miguel9554/dce-pfinal/simulaciones/informe/bw.asc

C1: cap; 1000µ
R1: res; 12k
R2: res; 470
RL: res; {RL}
V1: voltage; ""; AC 1
Ven: voltage; {Vcc}
Vep: voltage; {Vcc}
Vin: voltage; {V1}
Vip: voltage; {V1}
X7: amplificador
Named nets: Vcc, -Vcc, V-, 0, Vin, V+, Vo
.param V1=15 Vcc=30
.param RL=8
.ac dec 1000 1 200k
