miguel9554/dce-pfinal/simulaciones/informe/eficiencia.asc

C1: cap; 1000µ
R1: res; 12k
R2: res; 470
RL: res; {RL}
V1: voltage; SINE(0 {Vinpp/2} {fin})
Ven: voltage; {Vcc}
Vep: voltage; {Vcc}
Vin: voltage; {V1}
Vip: voltage; {V1}
X7: amplificador
Named nets: Vcc, -Vcc, V-, 0, Vin, V+, Vo
.param N_cycles_show=1 N_cycles_wait=10
.param Vinpp=2 fin=100
.param V1=15 Vcc=30
.param RL=8
.tran 0 {(N_cycles_wait+N_cycles_show)/fin} {N_cycles_wait/fin} {1/(fin*10e3)}
.meas TRAN P_Vep AVG -V(vcc)*I(Vep) FROM 0
.meas TRAN P_Ven AVG V(-vcc)*I(Ven) FROM 0
.meas TRAN P_Vip AVG -V(V+)*I(Vip) FROM 0
.meas TRAN P_Vin AVG V(V-)*I(Vin) FROM 0
.meas TRAN P_carga AVG V(vo)*I(RL) FROM 0
.meas TRAN P_fuentes PARAM P_Vep+P_Ven+P_Vip+P_Vin
.meas TRAN eficiencia PARAM P_carga/P_fuentes
.step param Vinpp list 0.17 0.21 0.33 0.71 0.96 1.16 1.42 1.64 1.73 1.86 02.02
