miguel9554/dce-pfinal/simulaciones/informe/imd.asc

C1: cap; 1000µ
R1: res; 12k
R2: res; 470
RL: res; {RL}
V1: voltage; SINE(0 {Vinpp/2} {fin}); Rser=1
V2: voltage; SINE(0 {4*Vinpp/2} {fsep})
Ven: voltage; {Vcc}
Vep: voltage; {Vcc}
Vin: voltage; {V1}
Vip: voltage; {V1}
X7: amplificador
Named nets: Vcc, -Vcc, V-, 0, Vin, V+, Vo
.param N_cycles_show=50 N_cycles_wait=50
.param Vinpp=0.1 fin=5k fsep=100
.param V1=15 Vcc=30
.param RL=8
.tran 0 {(N_cycles_wait+N_cycles_show)/fsep} {N_cycles_wait/fsep} {1/(fsep*10e3)}
.four {fin} 9 {N_cycles_show} V(Vo)
.OPTIONS plotwinsize=0 numdgt=7
.option noopiter
.meas TRAN P_carga AVG V(vo)*I(RL) FROM 0
