miguel9554/dce-pfinal/simulaciones/informe/psrr.asc

C1: cap; 1000µ
R1: res; 12k
R2: res; 470
RL: res; {RL}
Ven: voltage; {Vcc}
Vep: voltage; SINE({Vcc-App/2} {App/2} {f})
Vin: voltage; {V1}
Vip: voltage; {V1}
X7: amplificador
Named nets: Vcc, -Vcc, V-, 0, Vin, V+, Vo
.param N_cycles_show=1 N_cycles_wait=1
.param App=7 f=20
.param V1=15 Vcc=30
.param RL=8
.tran 0 {(N_cycles_wait+N_cycles_show)/f} {N_cycles_wait/f} {1/(f*10e3)}
