miguel9554/dce-pfinal/simulaciones/informe/sr.asc

C1: cap; 1000µ
R1: res; 12k
R2: res; 470
RL: res; {RL}
V1: voltage; PULSE(0 {Vinpp} {N_cycles_wait/fin} 1n 1n {1/(2*fin)} {1/(fin)}); Rser=1
Ven: voltage; {Vcc}
Vep: voltage; {Vcc}
Vin: voltage; {V1}
Vip: voltage; {V1}
X7: amplificador
Named nets: Vcc, -Vcc, V-, 0, Vin, V+, Vo
.param N_cycles_show=0.25 N_cycles_wait=5
.param Vinpp=0.4 fin=10k
.param V1=15 Vcc=30
.param RL=8
.tran 0 {(N_cycles_wait+N_cycles_show)/fin} {N_cycles_wait/fin} {1/(fin*10e3)}
