miguel9554/dce-pfinal/simulaciones/informe/thd.asc

C1: cap; 1000µ
R1: res; 12k
R2: res; 470
RL: res; {RL}
V1: voltage; SINE(0 {Vinpp/2} {fin})
Ven: voltage; {Vcc}
Vep: voltage; {Vcc}
Vin: voltage; {V1}
Vip: voltage; {V1}
X7: amplificador
Named nets: Vcc, -Vcc, V-, 0, Vin, V+, Vo
.param N_cycles_show=20 N_cycles_wait=10
.param Vinpp=2 fin=10k
.param V1=15 Vcc=30
.param RL=8
.step param Vinpp list 0.16 0.24 0.36 0.668 1.05 1.88 2
.tran 0 {(N_cycles_wait+N_cycles_show)/fin} {N_cycles_wait/fin} {1/(fin*10e3)}
.four {fin} 9 {N_cycles_show} V(Vo)
.OPTIONS plotwinsize=0 numdgt=15
.option noopiter
.meas TRAN P_carga AVG V(vo)*I(RL) FROM 0
