miguel9554/dce-pfinal/smps/simulaciones/fuente.asc

C1: cap; 2m; Rser=0.1
D1: schottky; 1N5819
L1: ind; 200µ
R1: res; {R1}
R2: res; {R2}
R3: res; {RL/6}
R4: res; {RL}
R5: res; 1µ
RL: res; {RL}
S1: sw; SWITCH
S2: sw; SWITCH
U1: LM2576_TRANS
V1: voltage; 30
V3: voltage; PULSE(0 30 {T_SWITCH} 1n 1n 10 20)
V4: voltage; 10
Named nets: 0, Vout, Vsw, Vfb
.tran 0 {T_SWITCH*2} 0
.param Vo=15 Io=1
.param RL=Vo/Io R1=3.3k R2=R1*(Vo-1.23)/1.23
.param Fs=52k Ts=1/Fs
.meas TRAN IL_mean AVG -I(L1) FROM 12m
.meas deltaI RMS -I(L1) - IL_mean FROM 12m
.model SWITCH SW(Ron=1m Roff=100Meg Vt=0 Vh=0)
Esta trabaja primero
Esta entra después
.param T_SWITCH=20m
este capacitor tiene que tener una ESR (resistencia equivalente serie) o sino el sistema es inestable
