miguel9554/dce-pfinal/simulaciones/total/total.asc

C1: cap; 47µ
C2: cap; 47µ
C3: cap; 47µ
C4: cap; 1000µ
C7: cap; 20n
Ccomp1: cap; {Ccomp}
D1: diode; 1N4148
D2: diode; 1N4148
D3: diode; 1N4148
D4: diode; 1N4148
D5: zener; 1N4728
D6: zener; 1N4728
Q1: npn; BC547B
Q2: pnp; BC557B
Q3: pnp; BC557B
Q4: npn; BC547B
Q5: npn; BC547B
Q6: pnp; BC557B
Q7: pnp; BC557B
Q8: pnp; BC557B
Q10: npn; BC547B
Q11: npn; BC547B
Q12: npn; BC547B
Q13: npn; BC547B
Q14: npn; BC547B
Q15: pnp; BC557B
Q16: pnp; BC557B
Q17: pnp; BC557B
Q18: pnp; BC557B
Q19: npn; BC547B
R1: res; {ReFte}
R2: res; {ReFte}
R3: res; 10
R4: res; {Rr2}
R5: res; {Rr1}
R6: res; {ReDif}
R7: res; {ReDif}
R8: res; 100
R9: res; 2.2k
R10: res; 68
R11: res; 10k
R12: res; 10k
R13: res; 2.2k
R15: res; {Rr1}
R16: res; 2.2k
R18: res; 0
R19: res; 0
R20: res; 200
R21: res; 8
R22: res; 100
R23: res; 100
R24: res; 100
R25: res; 100
R26: res; 16
R27: res; 3.3k
R28: res; 1.68k
V3: voltage; SINE(0 {Vin} {fin})
V5: voltage; {V1}
V6: voltage; {V1}
V7: voltage; {Vcc}
V8: voltage; {Vcc}
Named nets: 0, Vin, V+, V-, V1+, V1-, Vo
.tran 0 {(N_cycles_wait+N_cycles_show)/fin} {N_cycles_wait/fin} {1/(fin*10e3)}
.four {fin} 9 {N_cycles_show} V(Vo)
.OPTIONS plotwinsize=0 numdgt=15
.param N_cycles_show=4 N_cycles_wait=10
.param Vin=1 fin=10k
.param ReDif=100 ReFte=1
.param Rr1=9.6k Rr2=400
.param Ccomp=100p
.param V1=20 Vcc=30
.MODEL 1N4728 D( IS=15N N=2.22 BV=3.3 IBV=76M 
+      RS=169M CJO=4P VJ=750M M=330M FC=500M 
+      TT=100N EG=1.11 XTI=3 KF=0 AF=1 
+      )
