miguel9554/dce-pfinal/simulaciones/salida/salida.asc

C1: cap; 47µ
C2: cap; 47µ
C3: cap; 20n
D1: diode; 1N4148
D2: diode; 1N4148
D3: diode; 1N4148
D4: diode; 1N4148
D5: zener; 1N4728
D6: zener; 1N4728
Q1: npn; BC547B
Q2: npn; BC547B
Q3: npn; BC547B
Q4: npn; BC547B
Q5: pnp; BC557B
Q6: pnp; BC557B
Q7: pnp; BC557B
Q8: pnp; BC557B
Q9: npn; BC547B
Q10: pnp; BC557B
Q11: pnp; BC557B
Q12: pnp; BC557B
R1: res; 0
R2: res; 0
R3: res; 200
R4: res; 8
R5: res; 100
R6: res; 100
R7: res; 100
R8: res; 100
R9: res; 16
R10: res; 3.3k
R11: res; 1.68k
R12: res; 100
R13: res; 2.2k
R14: res; 2.2k
R15: res; 68
R16: res; 10k
R17: res; 10k
RL1: res; 1
V5: voltage; SINE(0 {Vin} {fin})
V6: voltage; {V1}
V7: voltage; {V1}
V8: voltage; {V2}
V9: voltage; {V2}
Named nets: 0, V1+, V1-, V2-, V2+, Vo, V+
.param V1=20 V2=30
.param Vin=25 fin=10k
;tran 0 {(N_cycles_wait+N_cycles_show)/fin} {N_cycles_wait/fin} {1/(fin*10e3)}
.param N_cycles_show=10 N_cycles_wait=10
.op 0 {(N_cycles_wait+N_cycles_show)/fin} {N_cycles_wait/fin} {1/(fin*10e3)}
.four {fin} 9 {N_cycles_show} V(Vo)
.OPTIONS plotwinsize=0 numdgt=15
.MODEL 1N4728 D( IS=15N N=2.22 BV=3.3 IBV=76M 
+      RS=169M CJO=4P VJ=750M M=330M FC=500M 
+      TT=100N EG=1.11 XTI=3 KF=0 AF=1 
+      )
