miguel9554/dce-pfinal/simulaciones/fte_corriente_ds/fte_corriente_ds.asc

C1: cap; 47µ
C2: cap; 47µ
Q1: pnp; BC557B
Q2: pnp; BC557B
Q3: pnp; BC557B
R2: res; 100
R3: res; 2.2k
R4: res; 10k
R5: res; 10k
R6: res; 2.2k
R7: res; 68
RL1: res; 1
RL2: res; 5k
V1: voltage; 25
Named nets: 0, V+
.op
