miguel9554/dce-pfinal/simulaciones/fte_corriente/fte_corriente.asc

Q1: pnp; BC557B
Q4: pnp; BC557B
Q5: pnp; BC557B
R1: res; 4.9k
R6: res; 10k
V1: voltage; 25
V2: voltage; -25
Named nets: 0, V+, V-
.op
