miguel9554/dce-pfinal/simulaciones/emisor_comun/emisor_comun.asc

Q6: npn; BC548B
R5: res; 1k
R10: res; 6.8k
R12: res; 3.9k
R13: res; 1k
V1: voltage; 25
V2: voltage; -25
V3: voltage; SINE(0 10m 10k)
Named nets: V+, V-, vin, 0
.INCLUDE ../BC548B.lib
.INCLUDE ../D1N4148.lib
.INCLUDE ../BC558B.lib
.tran 0 101m 100m 1u
