miguel9554/dce-pfinal/simulaciones/vas/vas.asc

Q6: npn; BC548B
Q7: npn; BC548B
R5: res; 1k
R8: res; 25k
R9: res; 5k
R10: res; 25k
R11: res; 10k
R12: res; 100k
R13: res; 125k
V1: voltage; 25
V2: voltage; -25
V3: voltage; SINE(0 10m 10k)
Named nets: V+, V-, vin, 0
.INCLUDE ../BC548B.lib
.INCLUDE ../D1N4148.lib
.INCLUDE ../BC558B.lib
.tran 0 101m 100m 1u
