miguel9554/dce-pfinal/simulaciones/sumador_vas/a/a.asc

C1: cap; 22n
C5: cap; 47µ
C6: cap; 47µ
C7: cap; {Cacop}
C8: cap; 1000µ
Ccomp1: cap; {Ccomp}
D1: diode; 1N4148
D2: diode; 1N4148
Q1: npn; mje340
Q9: npn; MPSA06
Q11: pnp; MPSA56
Q12: pnp; MPSA56
Q13: npn; MPSA06
Q14: npn; MPSA06
Q15: pnp; MPSA56
Q16: pnp; MPSA56
Q17: pnp; MPSA56
Q18: npn; MPSA06
R1: res; 10
R2: res; 3.3k
R3: res; 1.2k
R16: res; {ReFte}
R18: res; {ReFte}
R19: res; 10
R20: res; {Rr2}
R21: res; {Rr1}
R22: res; {ReDif}
R23: res; {ReDif}
R24: res; 47
R25: res; 2.2k
R26: res; 68
R27: res; 10k
R28: res; 10k
R29: res; 2.2k
R30: res; {Rr1}
R31: res; 2.2k
V4: voltage; SINE(0 {Vin} {fin})
V7: voltage; {Vcc}
V8: voltage; {Vcc}
Named nets: 0, Vin, V+, V-
.tran 0 {(N_cycles_wait+N_cycles_show)/fin} {N_cycles_wait/fin} {1/(fin*10e3)}
.four {fin} 9 {N_cycles_show} V(Vo)
.OPTIONS plotwinsize=0 numdgt=15
.param N_cycles_show=1 N_cycles_wait=10
.param Vin=100m fin=1k
.param ReDif=100 ReFte=68
.param Rr1=12k Rr2=470
.param Ccomp=100p Cacop=10u
.param Vcc=30
.MODEL MPSA56  PNP (
+ IS=120.32E-15
+ BF=188.84
+ VAF=100
+ IKF=2.8075
+ ISE=135.83E-15
+ NE=1.4750
+ BR=24.295
+ VAR=100
+ IKR=2.3092
+ ISC=703.00E-15
+ NC=1.6487
+ NK=1.3505
+ RB=1.9849
+ RC=24.680E-3
+ CJE=96.427E-12
+ VJE=.83382
+ MJE=.41469
+ CJC=52.708E-12
+ VJC=1.2213
+ MJC=.57874
+ TF=620.18E-12
+ XTF=49.825
+ VTF=22.355
+ ITF=.93852
+ TR=10.000E-9)
.MODEL MPSA06 npn
+IS=6.03149e-15 BF=559.138 NF=0.841146 VAF=996.086
+IKF=0.187838 ISE=1e-08 NE=3.53096 BR=43.984
+NR=0.893292 VAR=1.45264 IKR=1e-05 ISC=3.06474e-11
+NC=3.98114 RB=0.01 IRB=0.269152 RBM=0.01
+RE=1e-05 RC=0.000928752 XTB=1.17305 XTI=1
+EG=1.05 CJE=5.54912e-11 VJE=0.577764 MJE=0.313139
+TF=5.4629e-10 XTF=23.7458 VTF=7.07849 ITF=4.69733
+CJC=1.76218e-11 VJC=0.4 MJC=0.285166 XCJC=0.902334
+FC=0.732277 CJS=0 VJS=0.75 MJS=0.5
+TR=1e-07 PTF=0 KF=0 AF=1
.MODEL mje340 NPN(IS=1.03431e-13 BF=172.974 NF=0.939811 VAF=27.3487
+IKF=0.0260146 ISE=4.48447e-11 NE=1.61605 BR=16.6725 NR=0.796984
+VAR=6.11596 IKR=0.10004 ISC=9.99914e-14 NC=1.99995 RB=1.47761 IRB=0.2
+RBM=1.47761 RE=0.0001 RC=1.42228 XTB=2.70726 XTI=1 EG=1.206 CJE=1e-11
+VJE=0.75 MJE=0.33 TF=1e-09 XTF=1 VTF=10 ITF=0.01 CJC=1e-11 VJC=0.75
+MJC=0.33 XCJC=0.9 FC=0.5 CJS=0 VJS=0.75 MJS=0.5 TR=1e-07 PTF=0
+Vceo=300 Icrating=0.5A mfg=OnSemi)
