miguel9554/dce-pfinal/simulaciones/salida/generadores/generadores.asc

D1: diode; 1N4148
D2: diode; 1N4148
D3: diode; 1N4148
D4: diode; 1N4148
Q1: npn; BC547B
Q2: npn; BC547B
Q3: npn; BC547B
Q4: npn; BC547B
Q5: pnp; BC557B
Q6: pnp; BC557B
Q7: pnp; BC557B
Q8: pnp; BC557B
R1: res; 0
R2: res; 0
R3: res; 200
R4: res; 8
R5: res; 100
R6: res; 100
V1: voltage; SINE({Voffset} {Vin} {fin})
V2: voltage; 1.45
V3: voltage; 1.45
V4: voltage; 3.6
V5: voltage; 3.6
V6: voltage; {V1}
V7: voltage; {V1}
V8: voltage; {V2}
V9: voltage; {V2}
Named nets: 0, V1+, V1-, V2-, V2+, Vo, Vin
.param V1=20 V2=30
.param Vin=25 fin=10k Voffset=0
.tran 0 {(N_cycles_wait+N_cycles_show)/fin} {N_cycles_wait/fin} {1/(fin*10e3)}
.param N_cycles_show=10 N_cycles_wait=10
;op 0 {(N_cycles_wait+N_cycles_show)/fin} {N_cycles_wait/fin} {1/(fin*10e3)}
.four {fin} 9 {N_cycles_show} V(Vo)
.OPTIONS plotwinsize=0 numdgt=15
.MODEL 1N4728 D( IS=15N N=2.22 BV=3.3 IBV=76M 
+      RS=169M CJO=4P VJ=750M M=330M FC=500M 
+      TT=100N EG=1.11 XTI=3 KF=0 AF=1 
+      )
