miguel9554/dce-pfinal/simulaciones/sumador_vas/ganancia/sumador_vas.asc

C1: cap; 47µ
C2: cap; 47µ
Q1: pnp; BC557B
Q2: pnp; BC557B
Q3: npn; BC547B
Q4: pnp; BC557B
Q5: pnp; BC557B
Q6: pnp; BC557B
Q7: npn; BC547B
Q8: npn; BC547B
Q9: npn; BC547B
R1: res; 10
R2: res; {ReFte}
R3: res; {ReFte}
R4: res; {Rr1}
R5: res; {Rr2}
R6: res; 100
R7: res; {Rr1}
R8: res; 2.2k
R9: res; 68
R10: res; {ReDif}
R11: res; {ReDif}
R12: res; {Rr2}
R13: res; 10k
R14: res; 10k
R15: res; 2.2k
R16: res; 10k
V1: voltage; {Vcc}
V2: voltage; {-Vcc}
V3: voltage; SINE(0 {Vin} {fin})
Named nets: 0, Vin, V+, V-, Vo
.INCLUDE ../../D1N4148.lib
.tran 0 {(N_cycles_wait+N_cycles_show)/fin} {N_cycles_wait/fin} {1/(fin*1000)}
.four {fin} V(Vo)
.OPTIONS plotwinsize=0 numdgt=15
.param Vcc=30
.param N_cycles_show=20 N_cycles_wait=100
.param Vin=1 fin=10k
.param ReDif=100 ReFte=0.001
.param Rr1=9.6k Rr2=400
