miguel9554/dce-pfinal/simulaciones/buffer/av/av.asc

Q3: npn; BD135
Q6: npn; BD135
R8: res; 250
R34: res; 10
RL: res; 100k
Ro: res; 70k
V1: voltage; 20
V7: voltage; -5
Vo: voltage; 10
Named nets: 0, Vin, Vout
.INCLUDE ../../BD135.LIB
.ac dec 10000 1 100g
