miguel9554/dce-pfinal/simulaciones/buffer/ri/ri.asc

Q3: npn; BD135
Q6: npn; BD135
R1: res; 60k
R2: res; 10
R6: res; 250
RL: res; 5000g
V1: voltage; 20
V2: voltage; -5
V3: voltage; 10; AC 1
Named nets: 0, Vo, Vi
.INCLUDE ../../BD135.LIB
.ac dec 10000 1 100g
